howest-mct/2021-2022-projectone-DierickxBenno/ecg-test/ecg-test.ino

// Potentiometer is connected to GPIO 34 (Analog ADC1_CH6) 
const int potPin = 34;

// variable for storing the potentiometer value
float potValue = 0;

void setup() {
  Serial.begin(115200);
  delay(1000);
}

void loop() {
  // Reading potentiometer value
  potValue = analogRead(potPin);
  Serial.println((potValue/4095)*100);
  delay(500);
}
